fmcopaco/PacoMouse/images/cargador.png

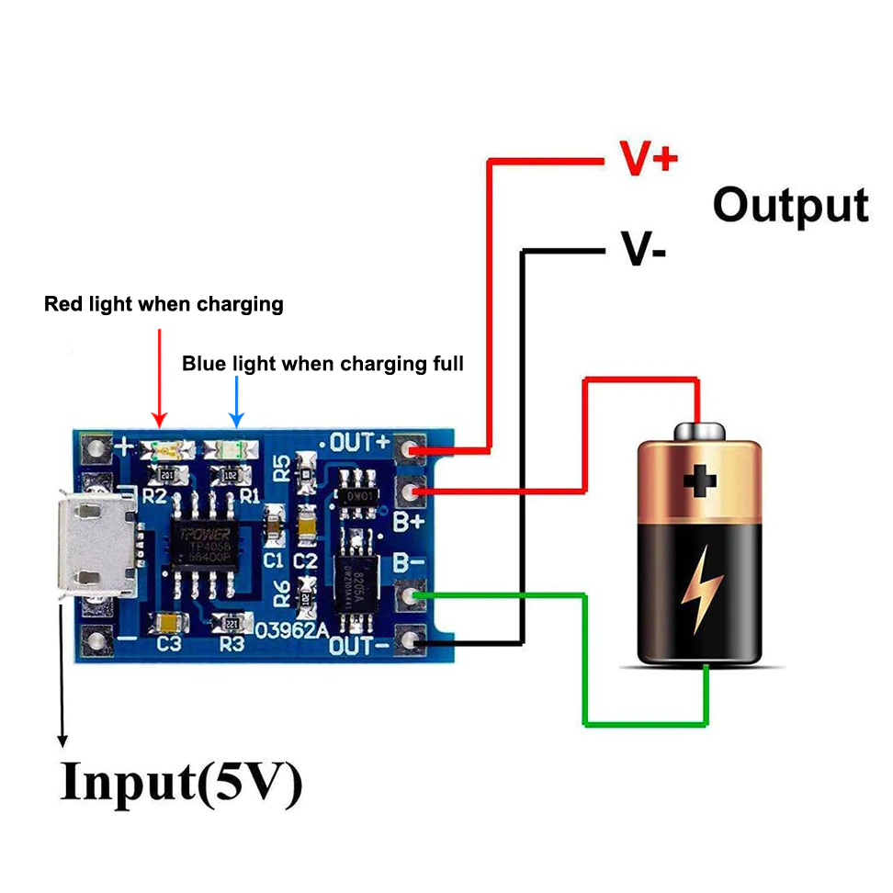
images/cargador.png
