fmcopaco/PacoMouse/images/DirSwitch.png

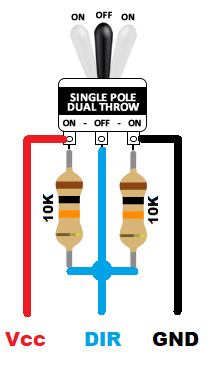
images/DirSwitch.png
