fmcopaco/PacoMouse/images/encoder_cond.jpg

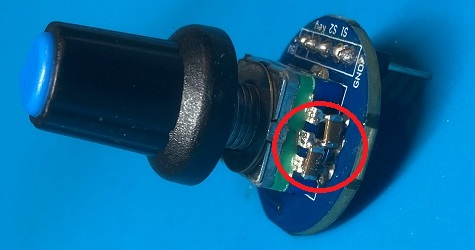
images/encoder_cond.jpg
