fmcopaco/PacoMouse/images/keypad_pcf8574.png

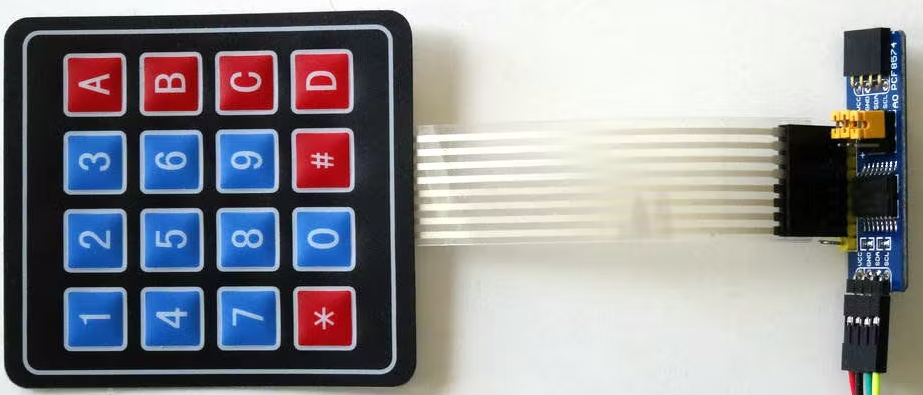
images/keypad_pcf8574.png
