fmcopaco/PacoMouse/images/OLED-128x64-Addresses.png

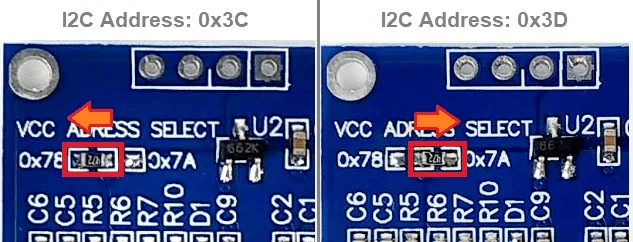
images/OLED-128x64-Addresses.png
