fmcopaco/PacoMouse/images/PacoMouse_Ard_Lnet_sch.png

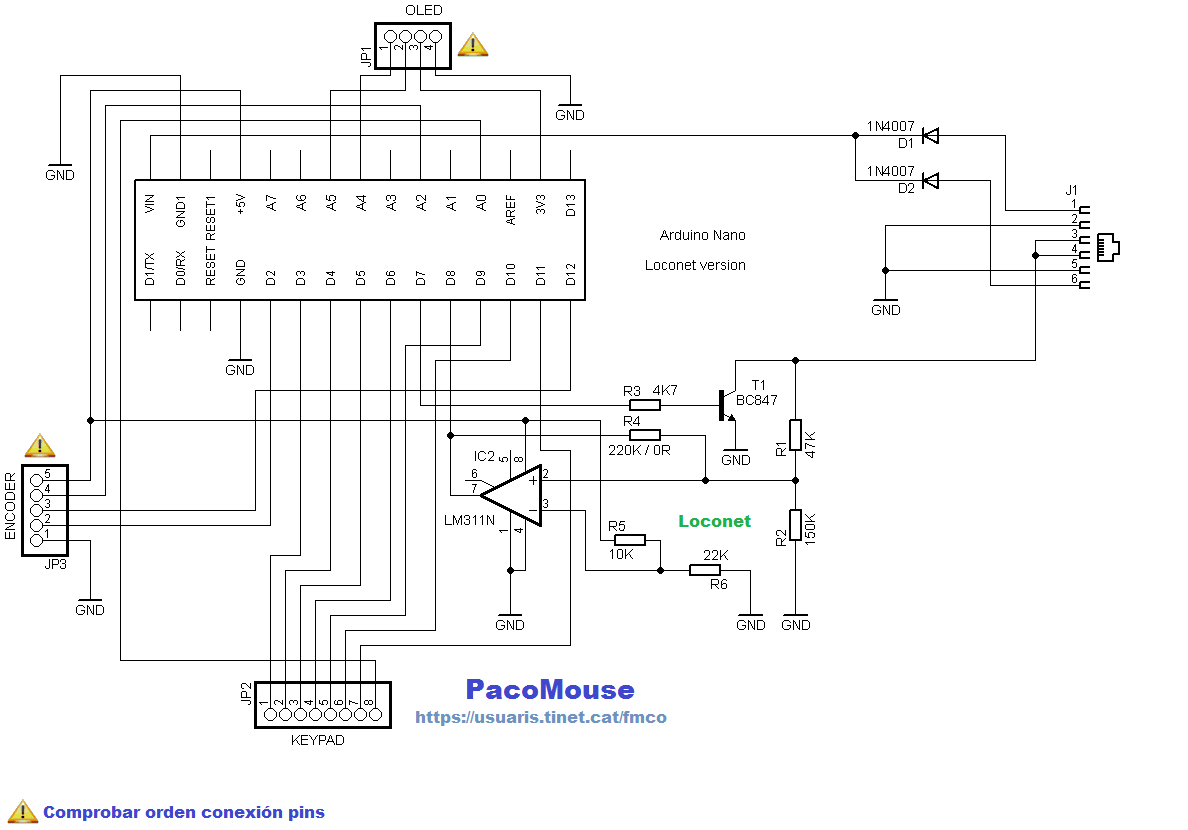
images/PacoMouse_Ard_Lnet_sch.png
