fmcopaco/PacoMouse/images/PacoMouse_Ard_Xnet_sch.png

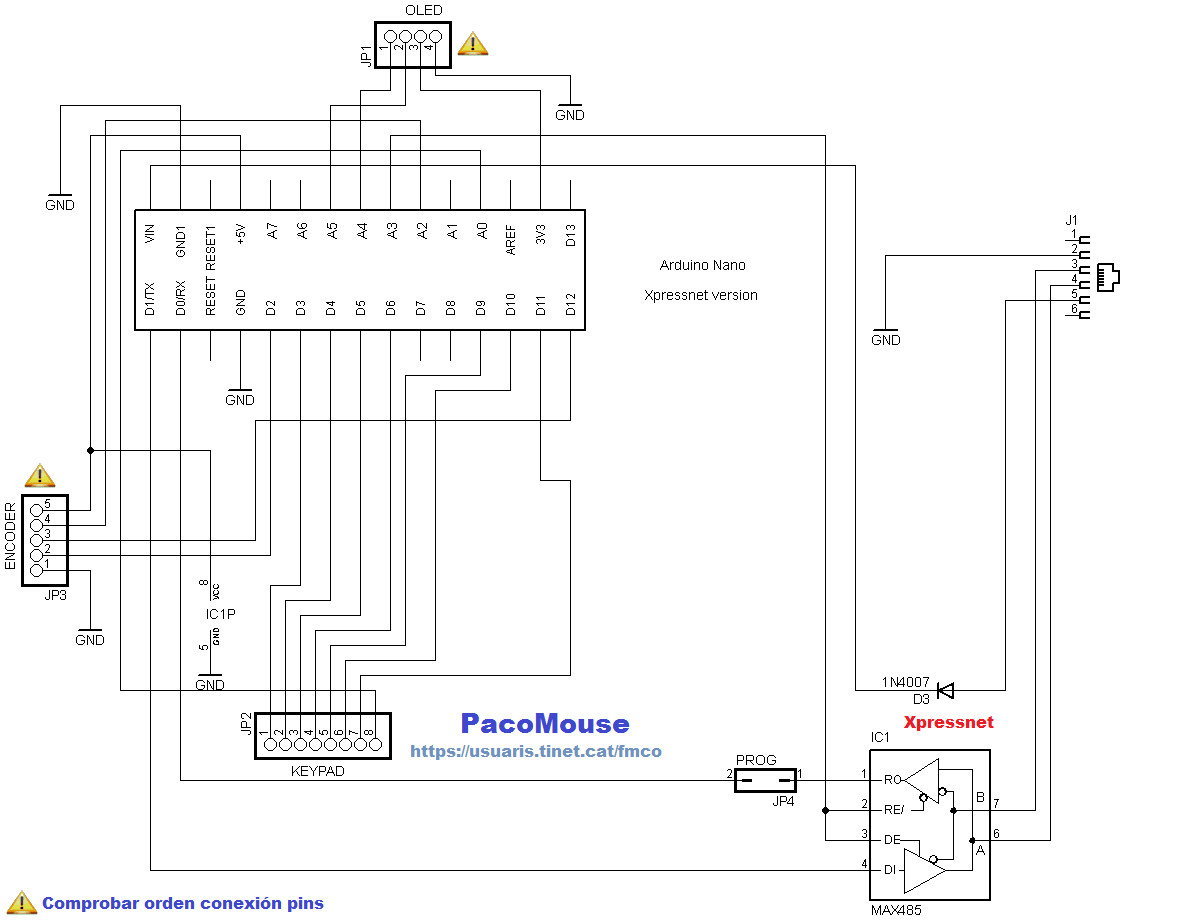
images/PacoMouse_Ard_Xnet_sch.png
