fmcopaco/PacoMouse/images/PacoMouse_lnet_R_sch.png

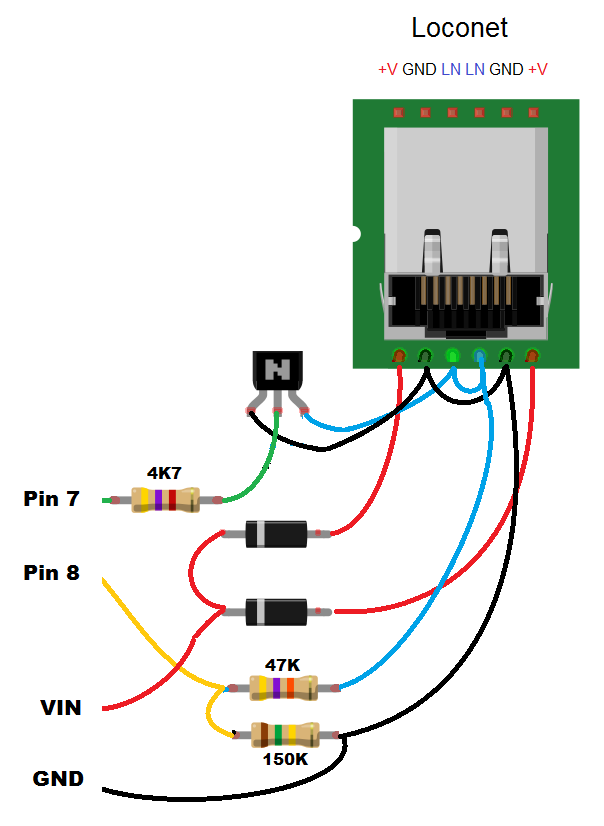
images/PacoMouse_lnet_R_sch.png
