fmcopaco/PacoMouse/images/PacoMouse_xnet_sch.png

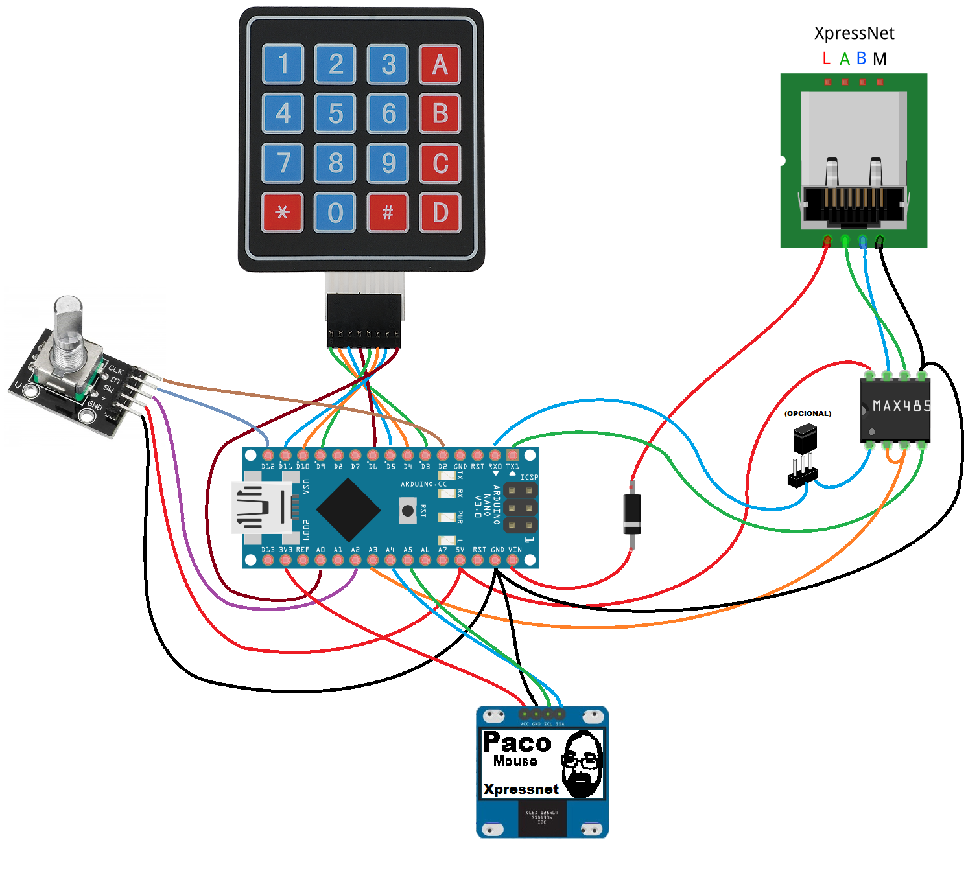
images/PacoMouse_xnet_sch.png
