fmcopaco/PacoMouse/images/pacoMouse_z21_sch.png

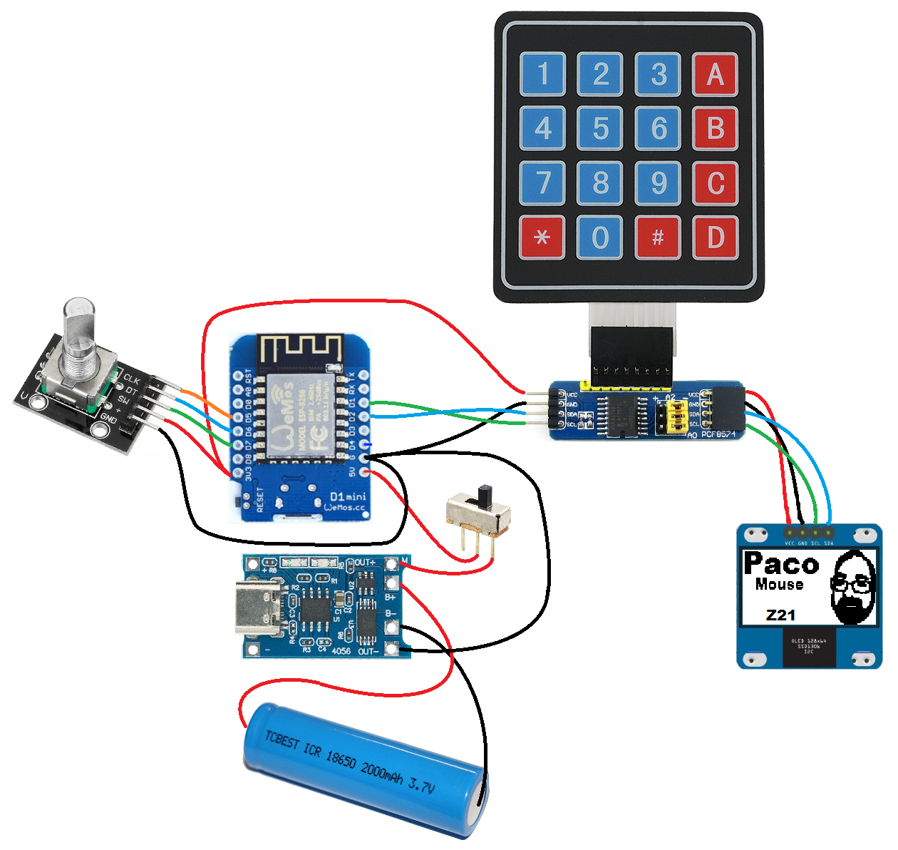
images/pacoMouse_z21_sch.png
