fmcopaco/PacoMouse/images/touchpad_50x45mm.png

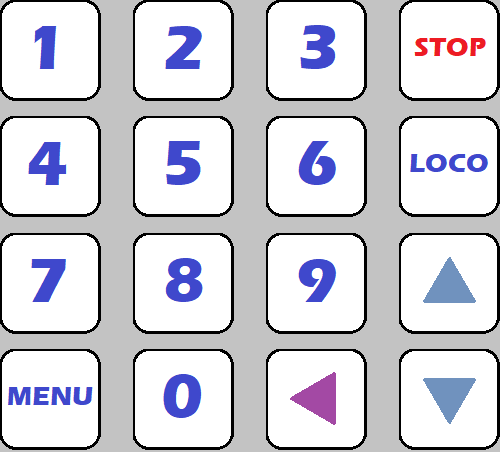
images/touchpad_50x45mm.png
