fmcopaco/PacoMouse/images/TTP229_TP2-jumper.png

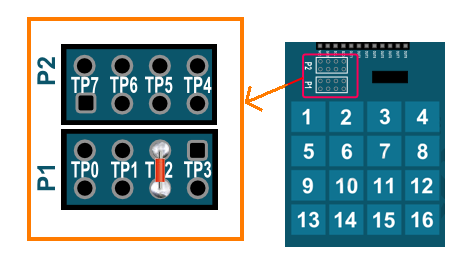
images/TTP229_TP2-jumper.png
