fmcopaco/PacoMouse/images/xnet_interface.png

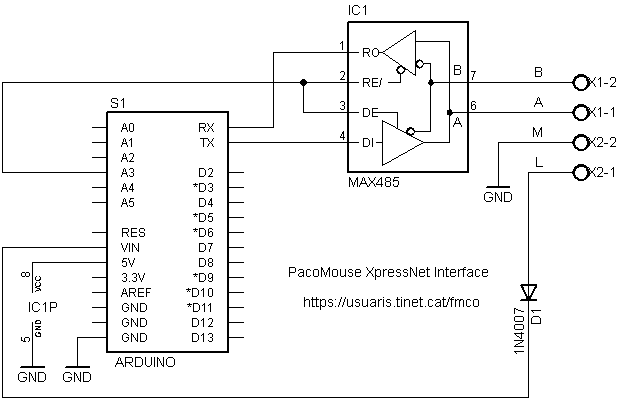
images/xnet_interface.png
