fmcopaco/PacoMouse/images/CS1_PacoMouse_wiring.png

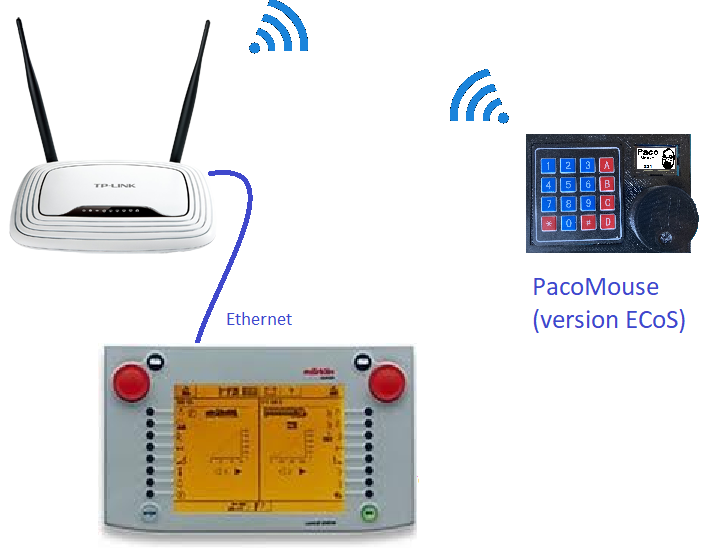
images/CS1_PacoMouse_wiring.png
