fmcopaco/PacoMouse/images/ECoS_PacoMouse_wiring.png

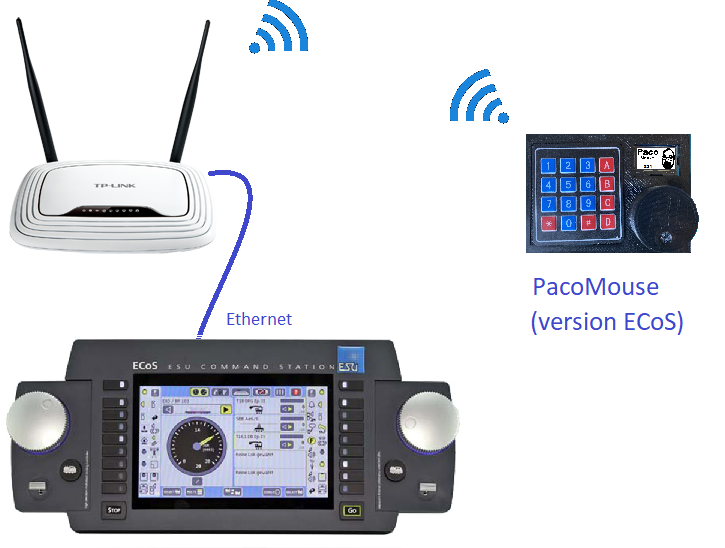
images/ECoS_PacoMouse_wiring.png
