fmcopaco/PacoMouse/images/YD_PacoMouse_wiring.png

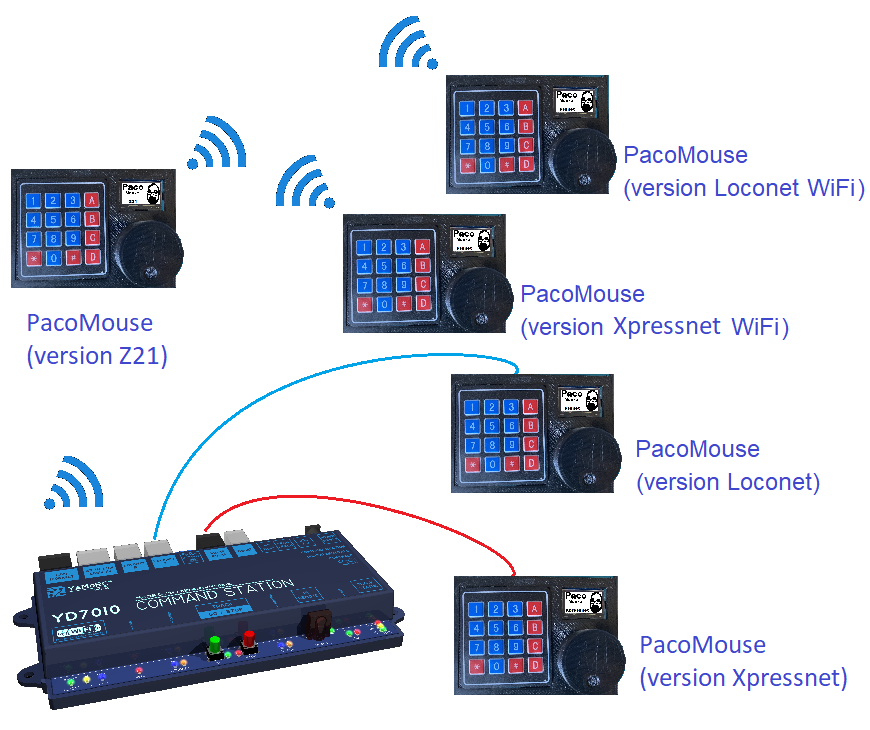
images/YD_PacoMouse_wiring.png
