fmcopaco/PacoMouse/images/Z21_black_PacoMouse_wiring.png

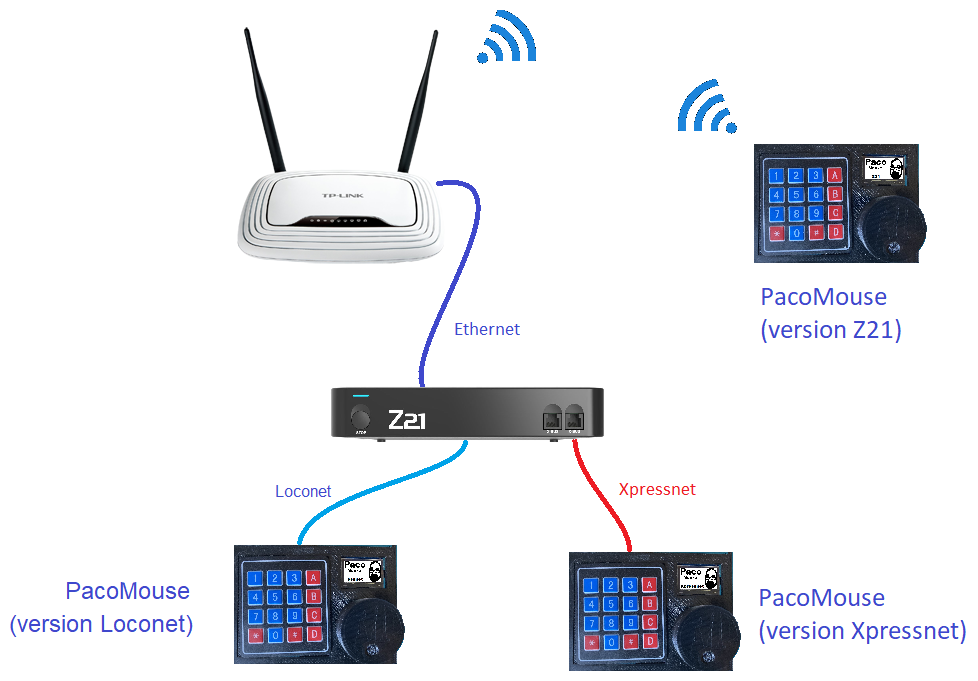
images/Z21_black_PacoMouse_wiring.png
