fmcopaco/PacoMouse/images/z21_white_PacoMouse_wiring.png

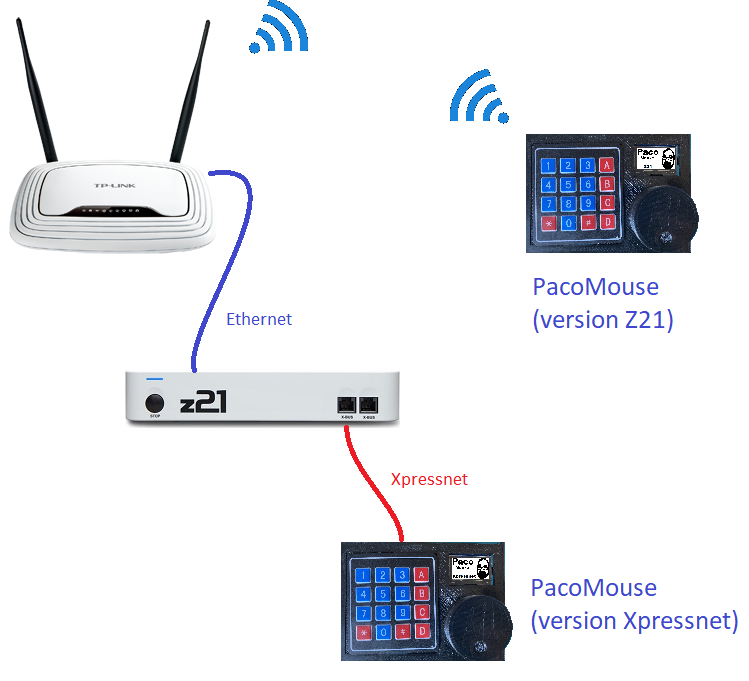
images/z21_white_PacoMouse_wiring.png
