fmcopaco/PacoMouse/images/LN_interface_test.png

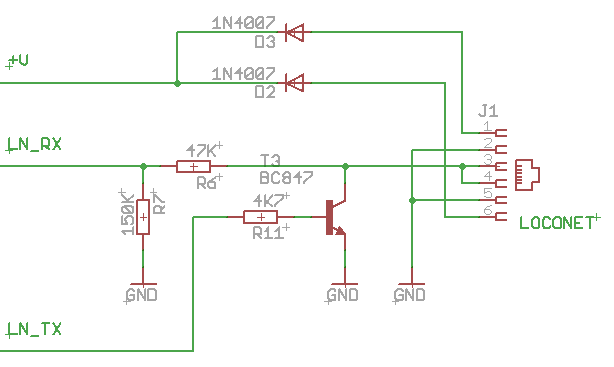
images/LN_interface_test.png
