fmcopaco/PacoMouse/src/Paco_Mouse/Num_15x31.h

/* Paco Mouse -- F. Cañada 2022-2025 --  https://usuaris.tinet.cat/fmco/
 
   Fixed width font for numbers & symbols

   This font is very useful when using overstrike as all characters & numbers
   are all the same width.

   This font also contains a few special characters that are nice for certain applications
   like clocks, signed values or decimal point values.

   The rendering code normally inserts a pad pixel so this size allows the font to fit
   perfectly on 32 and 64 tall glcd displays.

   Font has also been squeezed to 15 pixels wide for better alignment on 128 & 192 pixel displays.

   This file is part of the Paco Mouse project

*/

#ifndef NUM_15x31_H
#define NUM_15x31_H

GLCDFONTDECL(Num_15x31) = { // LCD Assistant (vertical)
  0x0, 0x0,	// size of zero indicates fixed width font
  15,		// width
  31,		// height
  '+',	// first char (48)
  21,		// char count

#if (TURNOUT_ICON == ONLY_TURN)
  // char '+' -> turnout diverge
  0x00, 0xFE, 0x02, 0x02, 0x02, 0x02, 0xFE, 0x00, 0x80, 0xC0, 0xE0, 0xE0, 0xC0, 0x80, 0x00,
  0x00, 0xFF, 0xE0, 0xF0, 0xF8, 0xFC, 0xFF, 0xFF, 0xFF, 0x7F, 0x3F, 0x1F, 0x0F, 0x07, 0x03,
  0x00, 0xFF, 0xFF, 0xFF, 0xFF, 0xFF, 0xFF, 0x01, 0x00, 0x00, 0x00, 0x00, 0x00, 0x00, 0x00,
  0x00, 0x1F, 0x1F, 0x1F, 0x1F, 0x1F, 0x1F, 0x00, 0x00, 0x00, 0x00, 0x00, 0x00, 0x00, 0x00,

  // char ',' -> turnout empty
  0x00, 0xFE, 0x02, 0x02, 0x02, 0x02, 0xFE, 0x00, 0x80, 0x40, 0x20, 0x20, 0x40, 0x80, 0x00,
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
  0xFF, 0xFF, 0xFF, 0xFF, 0xF0, 0xF0, 0xF0, 0xF0, 0xF0, 0x00, 0x00, 0x00, 0x00, 0x00, 0x00,
  0xFF, 0xFF, 0xFF, 0xFF, 0x00, 0x00, 0x00, 0x00, 0x00, 0x00, 0x00, 0x00, 0x00, 0x00, 0x00,
  0x0F, 0x0F, 0x0F, 0x0F, 0x00, 0x00, 0x00, 0x00, 0x00, 0x00, 0x00, 0x00, 0x00, 0x00, 0x00,

  // char '>' -> forward
  0x00, 0x00, 0x00, 0x00, 0x80, 0xE0, 0x38, 0xCE, 0x38, 0xE0, 0x80, 0x00, 0x00, 0x00, 0x00,
  0x80, 0xE0, 0x38, 0x4E, 0x73, 0x7C, 0x7F, 0x7F, 0x7F, 0x7C, 0x73, 0x4E, 0x38, 0xE0, 0x80,
  0x01, 0x01, 0x01, 0x01, 0x01, 0x01, 0x01, 0x01, 0x01, 0x01, 0x01, 0x01, 0x01, 0x01, 0x01,
  0x00, 0x00, 0x00, 0x00, 0x00, 0x00, 0x00, 0x00, 0x00, 0x00, 0x00, 0x00, 0x00, 0x00, 0x00,
  
  // char '?' -> question
  0x80, 0xC0, 0xE0, 0xE0, 0x70, 0x70, 0x70, 0x70, 0x70, 0x70, 0xE0, 0xE0, 0xC0, 0x80, 0x80,
  0x03, 0x03, 0x01, 0x00, 0x00, 0x00, 0x00, 0x00, 0x80, 0xC0, 0xE0, 0xF9, 0x7F, 0x3F, 0x0E,
  0x00, 0x00, 0x00, 0x00, 0x00, 0x9C, 0x9F, 0x9F, 0x07, 0x03, 0x01, 0x00, 0x00, 0x00, 0x00,
  0x00, 0x00, 0x00, 0x00, 0x00, 0x07, 0x07, 0x07, 0x00, 0x00, 0x00, 0x00, 0x00, 0x00, 0x00,

};

#endif
