fmcopaco/PacoMouse/src/Paco_Mouse/Sym_16x16.h

/* Paco Mouse -- F. Cañada 2022-2025 --  https://usuaris.tinet.cat/fmco/

   Fixed width font for symbols

   This font is very useful when using overstrike as all characters & numbers
   are all the same width.

   This font also contains a few special characters that are nice for certain applications
   like clocks, signed values or decimal point values.

   The rendering code normally inserts a pad pixel so this size allows the font to fit
   perfectly on 32 and 64 tall glcd displays.

   Font has also been squeezed to 15 pixels wide for better alignment on 128 & 192 pixel displays.

   This file is part of the Paco Mouse project

*/

#ifndef SYM_16x16_H
#define SYM_16x16_H

GLCDFONTDECL(Sym_16x16) = // LCD Assistant (vertical)
{
  0x0, 0x0,  // size of zero indicates fixed width font
  15,   // width  (will be 16 with pad pixel on right)
  15,   // height (will be 16 with pad pixel on bottom)
  '+',  // first char
  19,   // char count

  // char '+'
  0xE0, 0x18, 0xC4, 0xF2, 0xFA, 0xF9, 0xFD, 0xFD, 0xFD, 0xF9, 0xFA, 0xF2, 0xC4, 0x18, 0xE0, // Of
  0x03, 0x0C, 0x11, 0x27, 0x2F, 0x4F, 0x5F, 0x5F, 0x5F, 0x4F, 0x2F, 0x27, 0x11, 0x0C, 0x03,
  // char ','
  0x00, 0x00, 0x00, 0xC0, 0x20, 0xD0, 0xE8, 0xE8, 0xE8, 0xD0, 0x20, 0xC0, 0x00, 0x00, 0x00, //of
  0x00, 0x00, 0x00, 0x01, 0x02, 0x05, 0x0B, 0x0B, 0x0B, 0x05, 0x02, 0x01, 0x00, 0x00, 0x00,
  // char '-'
  0xE0, 0x18, 0x04, 0x02, 0x02, 0x01, 0x01, 0x01, 0x01, 0x01, 0x02, 0x02, 0x04, 0x18, 0xE0, // Ov
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
  //char 'W'
  0x00, 0x08, 0x1c, 0x3e, 0x7f, 0x1c, 0x1c, 0x1c, 0x1c, 0x1c, 0x3c, 0xf8, 0xf0, 0x00, 0x00, // loop
  0x00, 0x00, 0x00, 0x00, 0x00, 0x00, 0x00, 0x00, 0x30, 0x30, 0x30, 0x1f, 0x0f, 0x00, 0x00,

};

#endif
#endif
